DetectiveMittens/Cooee/Plastic Parts (FreeCAD)/Case2.SLDPRT

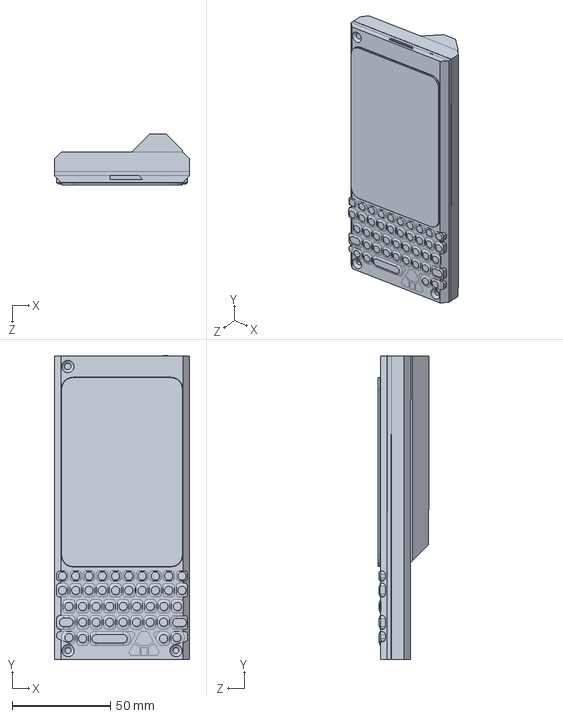
[picture p19: CAD file, 2026-03-17]
Plastic Parts (FreeCAD)/Case2.SLDPRT
68.8 x 154.6 x 25.8 mm
