DetectiveMittens/Cooee/Plastic Parts (FreeCAD)/Torch_Lens.SLDPRT

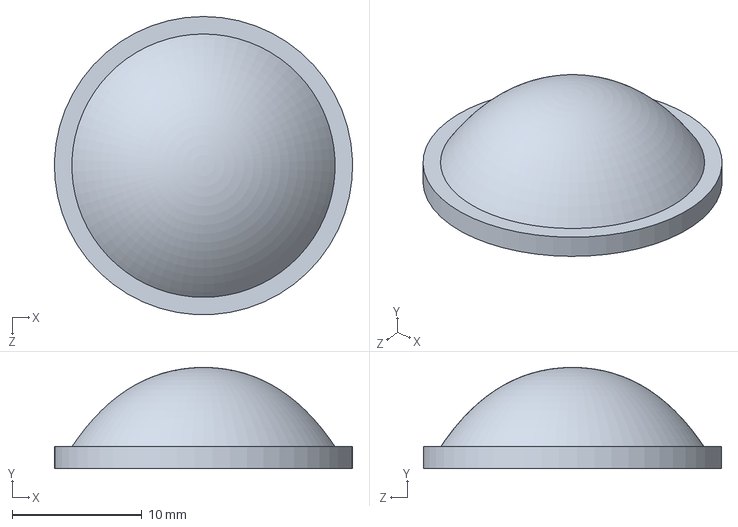
[picture p20: CAD file, 2026-03-17]
Plastic Parts (FreeCAD)/Torch_Lens.SLDPRT
23.0 x 7.80 x 23.0 mm
