DetectiveMittens/Cooee/Plastic Parts (FreeCAD)/Case.FCStd

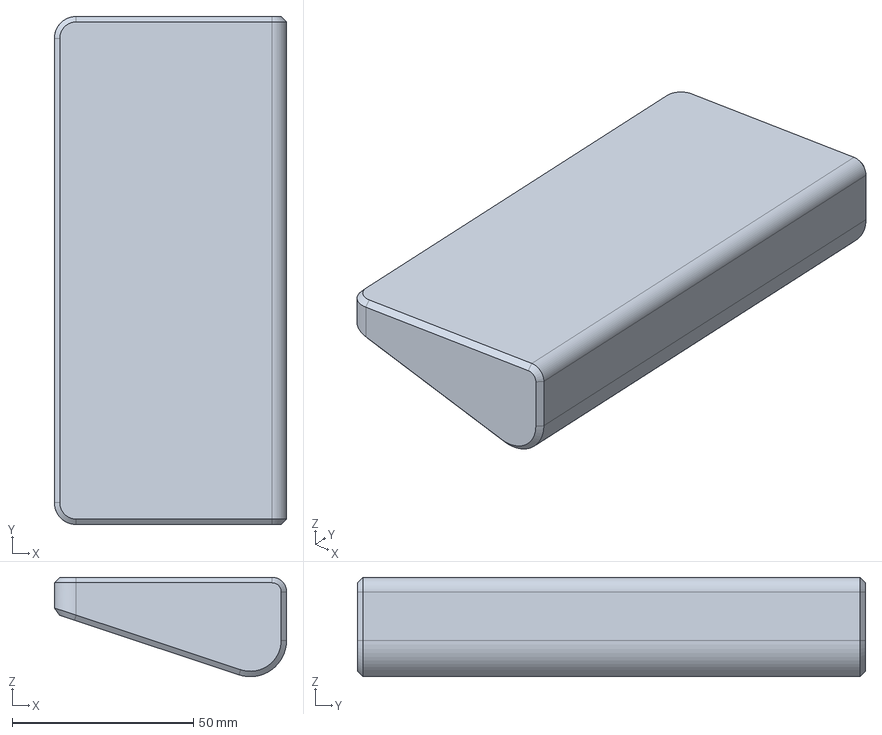
[picture p21: CAD file, 2026-01-19]
Plastic Parts (FreeCAD)/Case.FCStd
64.0 x 140.0 x 27.4 mm
