DetectiveMittens/Cooee/Plastic Parts (FreeCAD)/Motherboard_wScreen.FCStd

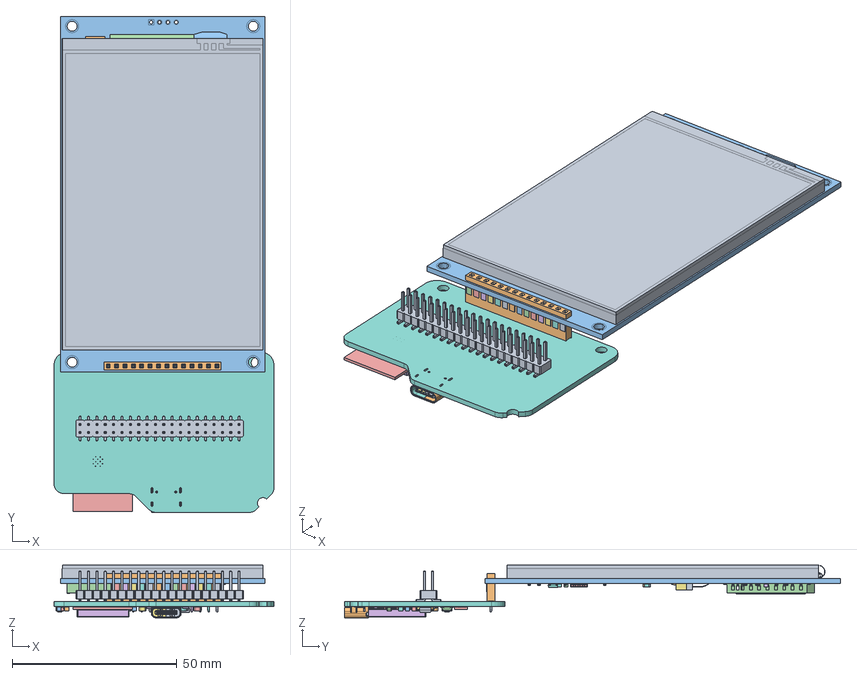
[picture p22: CAD file, 2026-01-19]
Plastic Parts (FreeCAD)/Motherboard_wScreen.FCStd
66.8 x 150.7 x 16.0 mm
PinHeader_2x20_P2.54mm_Vertical_SMD
PinSocket_1x14_P2.54mm_Vertical
Cooee_brains 1.3.1
Cooee_brains 1.3.001
Cooee_brains 1.3.002
Cooee_brains 1.3.003
Cooee_brains 1.3.004
Cooee_brains 1.3.005
Cooee_brains 1.3.006
Cooee_brains 1.3.007
Cooee_brains 1.3.008
Cooee_brains 1.3.009
Cooee_brains 1.3.010
Cooee_brains 1.3.011
Cooee_brains 1.3.012
Cooee_brains 1.3.013
Cooee_brains 1.3.014
Cooee_brains 1.3.015
Cooee_brains 1.3.016
Cooee_brains 1.3.017
Cooee_brains 1.3.018
Cooee_brains 1.3.019
Cooee_brains 1.3.020
Cooee_brains 1.3.021
Cooee_brains 1.3.022
Cooee_brains 1.3.023
Cooee_brains 1.3.024
Cooee_brains 1.3.025
Cooee_brains 1.3.026
Cooee_brains 1.3.027
Cooee_brains 1.3.028
Cooee_brains 1.3.029
Cooee_brains 1.3.030
Cooee_brains 1.3.031
Cooee_brains 1.3.032
Cooee_brains 1.3.033
Cooee_brains 1.3.034
Cooee_brains 1.3.035
Cooee_brains 1.3.036
Cooee_brains 1.3.037
Cooee_brains 1.3.038
Cooee_brains 1.3.039
Cooee_brains 1.3.040
Cooee_brains 1.3.041
Cooee_brains 1.3.042
Cooee_brains 1.3.043
Cooee_brains 1.3.044
Cooee_brains 1.3.045
Cooee_brains 1.3.046
Cooee_brains 1.3.047
Cooee_brains 1.3.048
Cooee_brains 1.3.049
Cooee_brains 1.3.050
Cooee_brains 1.3.051
Cooee_brains 1.3.052
Cooee_brains 1.3.053
Cooee_brains 1.3.054
Cooee_brains 1.3.055
Cooee_brains 1.3.056
Cooee_brains 1.3.057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
